mafleming/MultiMod-II/mecrisp-ice-2.7/common-verilog/usb_cdc/usb_cdc.v

//  USB 2.0 full speed Communications Device Class.
//  Written in verilog 2001

// USB_CDC module shall implement Full Speed (12Mbit/s) USB communications device
//   class (or USB CDC class) and Abstract Control Model (ACM) subclass.
// USB_CDC shall implement IN/OUT FIFO interface between USB and external APP module.

module usb_cdc
  #(parameter VENDORID = 16'h0000,
    parameter PRODUCTID = 16'h0000,
    parameter IN_BULK_MAXPACKETSIZE = 'd8,
    parameter OUT_BULK_MAXPACKETSIZE = 'd8,
    parameter BIT_SAMPLES = 'd4,
    parameter USE_APP_CLK = 0,
    parameter APP_CLK_RATIO = 'd4)
   (
    input        clk_i,
    input        rstn_i,

    // ---- to/from Application ------------------------------------
    input        app_clk_i,
    output [7:0] out_data_o,
    output       out_valid_o,
    // While out_valid_o is high, the out_data_o shall be valid and both
    //   out_valid_o and out_data_o shall not change until consumed.
    input        out_ready_i,
    // When both out_valid_o and out_ready_i are high, the out_data_o shall
    //   be consumed.
    input [7:0]  in_data_i,
    input        in_valid_i,
    // While in_valid_i is high, in_data_i shall be valid.
    output       in_ready_o,
    // When both in_ready_o and in_valid_i are high, in_data_i shall
    //   be consumed.

    // ---- to USB bus physical transmitters/receivers --------------
    output       tx_en_o,
    output       tx_dp_o,
    output       tx_dn_o,
    input        rx_dp_i,
    input        rx_dn_i
    );

   localparam    CTRL_MAXPACKETSIZE = 'd8;
   localparam [3:0] ENDP_CTRL = 'd0,
                    ENDP_BULK = 'd1,
                    ENDP_INT = 'd2;

   reg [1:0]        rstn_sq;

   wire [6:0]       addr;
   wire [3:0]       endp;
   wire [7:0]       out_data;
   wire [7:0]       in_data, ctrl_in_data, bulk_in_data;
   wire             out_valid;
   wire             in_req, ctrl_in_req, bulk_in_req;
   wire             in_zlp, ctrl_in_zlp;
   wire             in_valid, ctrl_in_valid, bulk_in_valid;
   wire             out_err;
   wire             out_nak, bulk_out_nak;
   wire             setup;
   wire             stall, ctrl_stall;
   wire             in_toggle_reset;
   wire             out_toggle_reset;
   wire             rstn, usb_reset;
   wire             in_ready, ctrl_in_ready, bulk_in_ready;
   wire             out_ready, ctrl_out_ready, bulk_out_ready;

   assign rstn = rstn_sq[0] & ~usb_reset;
   assign ctrl_in_ready = (endp == ENDP_CTRL) ? in_ready : 1'b0;
   assign ctrl_out_ready = (endp == ENDP_CTRL) ? out_ready : 1'b0;
   assign bulk_in_ready = (endp == ENDP_BULK) ? in_ready : 1'b0;
   assign bulk_out_ready = (endp == ENDP_BULK) ? out_ready : 1'b0;
   assign ctrl_in_req = (endp == ENDP_CTRL) ? in_req : 1'b0;
   assign bulk_in_req = (endp == ENDP_BULK) ? in_req : 1'b0;
   assign in_data = (endp == ENDP_CTRL) ? ctrl_in_data : bulk_in_data;
   assign in_zlp = (endp == ENDP_CTRL) ? ctrl_in_zlp : 1'b0;
   assign in_valid = (endp == ENDP_CTRL) ? ctrl_in_valid : ((endp == ENDP_BULK) ? bulk_in_valid : 1'b0);
   assign stall = (endp == ENDP_CTRL) ? ctrl_stall : 1'b0;
   assign out_nak = (endp == ENDP_BULK) ? bulk_out_nak : 1'b0;

   always @(posedge clk_i or negedge rstn_i) begin
      if (~rstn_i) begin
         rstn_sq <= 2'd0;
      end else begin
         rstn_sq <= {1'b1, rstn_sq[1]};
      end
   end

   sie #(.CTRL_MAXPACKETSIZE(CTRL_MAXPACKETSIZE),
         .IN_BULK_MAXPACKETSIZE(IN_BULK_MAXPACKETSIZE),
         .ENDP_CTRL(ENDP_CTRL),
         .ENDP_BULK(ENDP_BULK),
         .BIT_SAMPLES(BIT_SAMPLES))
   u_sie (.usb_reset_o(usb_reset),
          .tx_en_o(tx_en_o),
          .tx_dp_o(tx_dp_o),
          .tx_dn_o(tx_dn_o),
          .endp_o(endp),
       // .frame_o(),
          .out_data_o(out_data),
          .out_valid_o(out_valid),
          .out_err_o(out_err),
          .in_req_o(in_req),
          .setup_o(setup),
          .out_ready_o(out_ready),
          .in_ready_o(in_ready),
          .clk_i(clk_i),
          .rstn_i(rstn_sq[0]),
          .rx_dp_i(rx_dp_i),
          .rx_dn_i(rx_dn_i),
          .addr_i(addr),
          .in_valid_i(in_valid),
          .in_data_i(in_data),
          .in_zlp_i(in_zlp),
          .out_nak_i(out_nak),
          .stall_i(stall),
          .in_toggle_reset_i(in_toggle_reset),
          .out_toggle_reset_i(out_toggle_reset));

   ctrl_endp #(.VENDORID(VENDORID),
               .PRODUCTID(PRODUCTID),
               .CTRL_MAXPACKETSIZE(CTRL_MAXPACKETSIZE),
               .IN_BULK_MAXPACKETSIZE(IN_BULK_MAXPACKETSIZE),
               .OUT_BULK_MAXPACKETSIZE(OUT_BULK_MAXPACKETSIZE),
               .ENDP_BULK(ENDP_BULK),
               .ENDP_INT(ENDP_INT))
   u_ctrl_endp (.addr_o(addr),
                .in_data_o(ctrl_in_data),
                .in_zlp_o(ctrl_in_zlp),
                .in_valid_o(ctrl_in_valid),
                .stall_o(ctrl_stall),
                .in_toggle_reset_o(in_toggle_reset),
                .out_toggle_reset_o(out_toggle_reset),
                .clk_i(clk_i),
                .rstn_i(rstn),
                .out_data_i(out_data),
                .out_valid_i(out_valid),
                .out_err_i(out_err),
                .in_req_i(ctrl_in_req),
                .setup_i(setup),
                .out_ready_i(ctrl_out_ready),
                .in_ready_i(ctrl_in_ready));

   bulk_endp #(.IN_BULK_MAXPACKETSIZE(IN_BULK_MAXPACKETSIZE),
               .OUT_BULK_MAXPACKETSIZE(OUT_BULK_MAXPACKETSIZE),
               .BIT_SAMPLES(BIT_SAMPLES),
               .USE_APP_CLK(USE_APP_CLK),
               .APP_CLK_RATIO(APP_CLK_RATIO))
   u_bulk_endp (.in_data_o(bulk_in_data),
                .in_valid_o(bulk_in_valid),
                .app_in_ready_o(in_ready_o),
                .out_nak_o(bulk_out_nak),
                .app_out_valid_o(out_valid_o),
                .app_out_data_o(out_data_o),
                .clk_i(clk_i),
                .app_clk_i(app_clk_i),
                .rstn_i(rstn),
                .out_data_i(out_data),
                .out_valid_i(out_valid),
                .out_err_i(out_err),
                .in_req_i(bulk_in_req),
                .app_in_data_i(in_data_i),
                .app_in_valid_i(in_valid_i),
                .out_ready_i(bulk_out_ready),
                .in_ready_i(bulk_in_ready),
                .app_out_ready_i(out_ready_i));
endmodule
