mafleming/MultiMod-II/mecrisp-ice-2.7/multimod2/icestorm/j1a.v

`default_nettype none

`include "../common-verilog/j1-universal-16kb-quickstore.v"

`include "../common-verilog/usb_cdc/usb_cdc.v"
`include "../common-verilog/usb_cdc/bulk_endp.v"
`include "../common-verilog/usb_cdc/ctrl_endp.v"
`include "../common-verilog/usb_cdc/phy_rx.v"
`include "../common-verilog/usb_cdc/phy_tx.v"
`include "../common-verilog/usb_cdc/sie.v"

module top (
    input  clki,     // 48 MHz clock input
    output clki_en,  // Enable external clock

    inout  data_0, // Four user pins
    inout  data_1,
    inout  data_2,
    inout  data_3,

    output rgb0, // LED outputs
    output rgb1,
    output rgb2,

    output spi_cs,    // SPI Flash
    output spi_clk,
    inout  spi_miso,
    inout  spi_mosi,
    inout  spi_io2,
    inout  spi_io3,

    inout  usb_dp, // USB pins
    inout  usb_dn,
    output usb_dp_pu,
    input  usb_activ,

    output to71,   // Tristate buffer control
    output from71,
    output ctrl71,

    input  din71,  // HP71B bus control signals
    input  cdn71,
    input  strn71
);

  // ######   Clock   #########################################

  reg [1:0] divider;

  always @(posedge clki) divider <= divider + 1;

  wire clk_usb = clki;       // 48 MHz
  wire clk     = divider[1]; // 12 MHz

  assign clki_en = 1'b1;


  // ######   Reset logic   ###################################

  wire button = 1'b1;

  reg [7:0] reset_cnt = 0;
  wire resetq = &reset_cnt;

  always @(posedge clk) begin
    if (button) reset_cnt <= reset_cnt + !resetq;
    else        reset_cnt <= 0;
  end

  // ######   Bus   ###########################################

  wire io_rd, io_wr;
  wire [15:0] io_addr;
  wire [15:0] io_dout;
  wire [15:0] io_din;

  reg interrupt = 0;

  // ######   Processor   #####################################

  j1 #( .MEMWORDS(7680) ) _j1( // 15 kb Memory

    .clk(clk),
    .resetq(resetq),

    .io_rd(io_rd),
    .io_wr(io_wr),
    .io_dout(io_dout),
    .io_din(io_din),
    .io_addr(io_addr),

    .interrupt_request(interrupt)
  );

  // ######   SPI   ###########################################
  // M. Fleming
  // Make the SPI IO0~IO3 lines directional

  reg  [3:0] spio_dir = 4'b1110;   // 1:output, 0:input
  reg  [3:0] spio_out;
  wire [3:0] spio_in;

  SB_IO #(.PIN_TYPE(6'b1010_01)) spio0 (.PACKAGE_PIN(spi_miso), .D_OUT_0(spio_out[0]), .D_IN_0(spio_in[0]), .OUTPUT_ENABLE(spio_dir[0]));
  SB_IO #(.PIN_TYPE(6'b1010_01)) spio1 (.PACKAGE_PIN(spi_mosi), .D_OUT_0(spio_out[1]), .D_IN_0(spio_in[1]), .OUTPUT_ENABLE(spio_dir[1]));
  SB_IO #(.PIN_TYPE(6'b1010_01)) spio2 (.PACKAGE_PIN(spi_io2), .D_OUT_0(spio_out[2]), .D_IN_0(spio_in[2]), .OUTPUT_ENABLE(spio_dir[2]));
  SB_IO #(.PIN_TYPE(6'b1010_01)) spio3 (.PACKAGE_PIN(spi_io3), .D_OUT_0(spio_out[3]), .D_IN_0(spio_in[3]), .OUTPUT_ENABLE(spio_dir[3]));

  // ######   Warm Boot Control   #############################
  // M. Fleming
  // Add control register to j1a address space

   reg [2:0] BOOTCTL = 0;

  SB_WARMBOOT B_WARMBOOT(
      .BOOT(BOOTCTL[2]),
      .S0(BOOTCTL[0]),
      .S1(BOOTCTL[1])
  );


  // ######   HP-71B Bus Control   ############################
  // M. Fleming
  // No need to add control signals to j1a address space
  // Buffers are controlled by HP-71B bus state machine

   wire [2:0] BUFCTRL = 0;
   assign BUFCTRL = {to71, from71, ctrl71};


  // ######   HP-71B Bank Control   ###########################
  // M. Fleming
  // Bank control registers selected by the lower three I/O
  // address bits and enabled by the I/O address bit 10   assign read_bank = {inuse, chain, type[1:0]};

  // Bank bits are: InUse, ChainEnd, ROMtype[1:0]
   reg [3:0]  bank0 = 0;
   reg [3:0]  bank1 = 0;
   reg [3:0]  bank2 = 0;
   reg [3:0]  bank3 = 0;
   reg [3:0]  bank4 = 0;
   reg [3:0]  bank5 = 0;
   reg [3:0]  bank6 = 0;
   reg [3:0]  bank7 = 0;


   
  // ######   Ticks   #########################################

  reg [15:0] ticks;

  wire [16:0] ticks_plus_1 = ticks + 1;

  always @(posedge clk)
    if (io_wr & io_addr[14])
      ticks <= io_dout;
    else
      ticks <= ticks_plus_1;

  always @(posedge clk) // Generate interrupt on ticks overflow
    interrupt <= ticks_plus_1[16];

  // ######   Cycles   ########################################

  reg [15:0] cycles;

  always @(posedge clk) cycles <= cycles + 1;

  // ######   DATA   ##########################################
  // M. Fleming
  // These are currently controlled by the j1a CPU but will
  // eventually be part of the HP-71B bus state machine

  reg  [3:0] data_dir;   // 1:output, 0:input
  reg  [3:0] data_out;
  wire [3:0] data_in;

  SB_IO #(.PIN_TYPE(6'b1010_01)) io0 (.PACKAGE_PIN(data_0), .D_OUT_0(data_out[0]), .D_IN_0(data_in[0]), .OUTPUT_ENABLE(data_dir[0]));
  SB_IO #(.PIN_TYPE(6'b1010_01)) io1 (.PACKAGE_PIN(data_1), .D_OUT_0(data_out[1]), .D_IN_0(data_in[1]), .OUTPUT_ENABLE(data_dir[1]));
  SB_IO #(.PIN_TYPE(6'b1010_01)) io2 (.PACKAGE_PIN(data_2), .D_OUT_0(data_out[2]), .D_IN_0(data_in[2]), .OUTPUT_ENABLE(data_dir[2]));
  SB_IO #(.PIN_TYPE(6'b1010_01)) io3 (.PACKAGE_PIN(data_3), .D_OUT_0(data_out[3]), .D_IN_0(data_in[3]), .OUTPUT_ENABLE(data_dir[3]));

  // ######   SRAM   ##########################################

  reg  [15:0] sram_addr;

  wire sram_wr = io_wr & io_addr[7];

  wire [15:0] sram_in_bank0, sram_in_bank1, sram_in_bank2, sram_in_bank3;

    SB_SPRAM256KA rambank0 (
        .DATAIN(io_dout),
        .ADDRESS(sram_addr[13:0]),
        .MASKWREN(4'b1111),
        .WREN(sram_wr),
        .CHIPSELECT(1'b1),
        .CLOCK(clk),
        .STANDBY(1'b0),
        .SLEEP(~(sram_addr[15:14] == 2'b00)),
        .POWEROFF(1'b1),
        .DATAOUT(sram_in_bank0)
);

    SB_SPRAM256KA rambank1 (
        .DATAIN(io_dout),
        .ADDRESS(sram_addr[13:0]),
        .MASKWREN(4'b1111),
        .WREN(sram_wr),
        .CHIPSELECT(1'b1),
        .CLOCK(clk),
        .STANDBY(1'b0),
        .SLEEP(~(sram_addr[15:14] == 2'b01)),
        .POWEROFF(1'b1),
        .DATAOUT(sram_in_bank1)
);

    SB_SPRAM256KA rambank2 (
        .DATAIN(io_dout),
        .ADDRESS(sram_addr[13:0]),
        .MASKWREN(4'b1111),
        .WREN(sram_wr),
        .CHIPSELECT(1'b1),
        .CLOCK(clk),
        .STANDBY(1'b0),
        .SLEEP(~(sram_addr[15:14] == 2'b10)),
        .POWEROFF(1'b1),
        .DATAOUT(sram_in_bank2)
);

    SB_SPRAM256KA rambank3 (
        .DATAIN(io_dout),
        .ADDRESS(sram_addr[13:0]),
        .MASKWREN(4'b1111),
        .WREN(sram_wr),
        .CHIPSELECT(1'b1),
        .CLOCK(clk),
        .STANDBY(1'b0),
        .SLEEP(~(sram_addr[15:14] == 2'b11)),
        .POWEROFF(1'b1),
        .DATAOUT(sram_in_bank3)
);

  wire [15:0] sram_in = sram_in_bank3 | sram_in_bank2 | sram_in_bank1 | sram_in_bank0;

  // ######   USB-CDC terminal   ##############################

  assign usb_dp_pu = resetq;     // Pull-up on USB-P
   
  wire usb_p_tx;
  wire usb_n_tx;
  wire usb_p_rx;
  wire usb_n_rx;
  wire usb_tx_en;

   SB_IO #(
       .PIN_TYPE(6'b 1010_01), // PIN_OUTPUT_TRISTATE - PIN_INPUT
       .PULLUP(1'b 0)
   ) iobuf_usbp (
       .PACKAGE_PIN(usb_dp),
       .OUTPUT_ENABLE(usb_tx_en),
       .D_OUT_0(usb_p_tx),
       .D_IN_0(usb_p_rx)
   );

   SB_IO #(
       .PIN_TYPE(6'b 1010_01), // PIN_OUTPUT_TRISTATE - PIN_INPUT
       .PULLUP(1'b 0)
   ) iobuf_usbn (
       .PACKAGE_PIN(usb_dn),
       .OUTPUT_ENABLE(usb_tx_en),
       .D_OUT_0(usb_n_tx),
       .D_IN_0(usb_n_rx)
   );

  usb_cdc #(.VENDORID(16'h0483), .PRODUCTID(16'h5740), .BIT_SAMPLES(4), .USE_APP_CLK(1), .APP_CLK_RATIO(4)) _terminal
  (
    // Part running on 48 MHz:

    .clk_i(clk_usb),
    .tx_en_o(usb_tx_en),
    .tx_dp_o(usb_p_tx),
    .tx_dn_o(usb_n_tx),
    .rx_dp_i(usb_p_rx),
    .rx_dn_i(usb_n_rx),

    // Part running on 12 MHz:

    .app_clk_i(clk),
    .rstn_i(resetq),

    .out_data_o(terminal_data),
    .out_valid_o(terminal_valid),
    .out_ready_i(terminal_rd),

    .in_data_i(io_dout[7:0]),
    .in_ready_o(terminal_ready),
    .in_valid_i(terminal_wr)
  );

  wire terminal_valid, terminal_ready;
  wire [7:0] terminal_data;
  wire terminal_wr = io_wr & io_addr[12];
  wire terminal_rd = io_rd & io_addr[12];

  // ######   RING OSCILLATOR   ###############################

  wire [1:0] buffers_in, buffers_out;
  assign buffers_in = {buffers_out[0:0], ~buffers_out[1]};
  SB_LUT4 #(
          .LUT_INIT(16'd2)
  ) buffers [1:0] (
          .O(buffers_out),
          .I0(buffers_in),
          .I1(1'b0),
          .I2(1'b0),
          .I3(1'b0)
  );

  wire random = ~buffers_out[1];

  // ######   Blink   #########################################

  // Instantiate iCE40 LED driver hard logic.
  //
  // Note that it's possible to drive the LEDs directly,
  // however that is not current-limited and results in
  // overvolting the red LED.
  //
  // See also:
  // https://www.latticesemi.com/-/media/LatticeSemi/Documents/ApplicationNotes/IK/ICE40LEDDriverUsageGuide.ashx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

  reg [2:0] LEDS;

  SB_RGBA_DRV #(
      .CURRENT_MODE("0b1"),       // half current
      .RGB0_CURRENT("0b000011"),  // 4 mA
      .RGB1_CURRENT("0b000011"),  // 4 mA
      .RGB2_CURRENT("0b000011")   // 4 mA
  ) RGBA_DRIVER (
      .CURREN(1'b1),
      .RGBLEDEN(1'b1),
      .RGB1PWM(LEDS[0]),     // Red
      .RGB0PWM(LEDS[1]),     // Green
      .RGB2PWM(LEDS[2]),     // Blue
      .RGB0(rgb0),
      .RGB1(rgb1),
      .RGB2(rgb2)
  );


  // ######   IO Ports   ######################################

  /*        Bit READ            WRITE

    + ...0                      Write as usual
    + ...1                      _C_lear bits
    + ...2                      _S_et bits
    + ...3                      _T_oggle bits

      0008  3   LEDS            LEDS (cst)

      0010  4   IN                          Input
      0020  5   OUT             OUT (cst)   Output
      0040  6   DIR             DIR (cst)   Direction
      0080  7   SRAM read       SRAM write

      0100  8   SPI read        SPI write
      0101                      SPIO direction
      0200  9   USB status      Warm Boot write
      0400  10  Bank control    Bank control
      0800  11  SRAM addr       SRAM addr

      1000  12  UART RX         UART TX
      2000  13  UART Flags
      4000  14  Ticks           Set Ticks
      8000  15  Cycles
  */

  assign io_din =

    (io_addr[ 3] ? {13'd0, LEDS}                                                    : 16'd0) |

    (io_addr[ 4] ? {12'd0, data_in}                                                 : 16'd0) |
    (io_addr[ 5] ? {12'd0, data_out}                                                : 16'd0) |
    (io_addr[ 6] ? { 8'd0, spio_dir, data_dir}                                      : 16'd0) |
    (io_addr[ 7] ?         sram_in                                                  : 16'd0) |

    (io_addr[ 8] ? {12'd0, spio_in}                                                 : 16'd0) |
    (io_addr[ 9] ? {13'd0, usb_activ, usb_p_tx, usb_n_tx}                           : 16'd0) |
/*  Only needed during development */
    ((io_addr[10] & (io_addr[2:0] == 0)) ? {12'd0, bank0}                           : 16'd0) |
    ((io_addr[10] & (io_addr[2:0] == 1)) ? {12'd0, bank1}                           : 16'd0) |
    ((io_addr[10] & (io_addr[2:0] == 2)) ? {12'd0, bank2}                           : 16'd0) |
    ((io_addr[10] & (io_addr[2:0] == 3)) ? {12'd0, bank3}                           : 16'd0) |
    ((io_addr[10] & (io_addr[2:0] == 4)) ? {12'd0, bank4}                           : 16'd0) |
    ((io_addr[10] & (io_addr[2:0] == 5)) ? {12'd0, bank5}                           : 16'd0) |
    ((io_addr[10] & (io_addr[2:0] == 6)) ? {12'd0, bank6}                           : 16'd0) |
    ((io_addr[10] & (io_addr[2:0] == 7)) ? {12'd0, bank7}                           : 16'd0) |
/**/
    (io_addr[11] ?         sram_addr                                                : 16'd0) |

    (io_addr[12] ? { 8'd0, terminal_data}                                           : 16'd0) |
    (io_addr[13] ? {13'd0, random, terminal_valid, terminal_ready}                  : 16'd0) |
    (io_addr[14] ?         ticks                                                    : 16'd0) |
    (io_addr[15] ?         cycles                                                   : 16'd0) ;

  always @(posedge clk) begin

    if (io_wr & io_addr[3] & (io_addr[1:0] == 0))  LEDS  <=           io_dout;
    if (io_wr & io_addr[3] & (io_addr[1:0] == 1))  LEDS  <=  LEDS  & ~io_dout; // Clear
    if (io_wr & io_addr[3] & (io_addr[1:0] == 2))  LEDS  <=  LEDS  |  io_dout; // Set
    if (io_wr & io_addr[3] & (io_addr[1:0] == 3))  LEDS  <=  LEDS  ^  io_dout; // Invert

    if (io_wr & io_addr[5] & (io_addr[1:0] == 0))  data_out  <=               io_dout;
    if (io_wr & io_addr[5] & (io_addr[1:0] == 1))  data_out  <=  data_out  & ~io_dout; // Clear
    if (io_wr & io_addr[5] & (io_addr[1:0] == 2))  data_out  <=  data_out  |  io_dout; // Set
    if (io_wr & io_addr[5] & (io_addr[1:0] == 3))  data_out  <=  data_out  ^  io_dout; // Invert

    if (io_wr & io_addr[6] & (io_addr[1:0] == 0))  data_dir  <=               io_dout;
    if (io_wr & io_addr[6] & (io_addr[1:0] == 1))  data_dir  <=  data_dir  & ~io_dout; // Clear
    if (io_wr & io_addr[6] & (io_addr[1:0] == 2))  data_dir  <=  data_dir  |  io_dout; // Set
    if (io_wr & io_addr[6] & (io_addr[1:0] == 3))  data_dir  <=  data_dir  ^  io_dout; // Invert

    if (io_wr & io_addr[8] & (io_addr[1:0] == 0))  {spi_clk, spi_cs, spio_out}  <= io_dout;
    if (io_wr & io_addr[8] & (io_addr[1:0] == 1))  spio_dir                     <= io_dout;

    if (io_wr & io_addr[9]) BOOTCTL                <= io_dout;
    if (io_wr & io_addr[10] & (io_addr[2:0] == 0)) bank0   <= io_dout;
    if (io_wr & io_addr[10] & (io_addr[2:0] == 1)) bank1   <= io_dout;
    if (io_wr & io_addr[10] & (io_addr[2:0] == 2)) bank2   <= io_dout;
    if (io_wr & io_addr[10] & (io_addr[2:0] == 3)) bank3   <= io_dout;
    if (io_wr & io_addr[10] & (io_addr[2:0] == 4)) bank4   <= io_dout;
    if (io_wr & io_addr[10] & (io_addr[2:0] == 5)) bank5   <= io_dout;
    if (io_wr & io_addr[10] & (io_addr[2:0] == 6)) bank6   <= io_dout;
    if (io_wr & io_addr[10] & (io_addr[2:0] == 7)) bank7   <= io_dout;

    if (io_wr & io_addr[11]) sram_addr <= io_dout;
  end

endmodule
