mafleming/MultiMod-II/mecrisp-ice-2.7/common-verilog/j1-universal-32bit-singleport.v

`default_nettype none

`include "../common-verilog/stack2.v"

module j1(
  input wire clk,
  input wire resetq,

  output wire io_rd,
  output wire io_wr,
  output wire [31:0] io_addr,
  output wire [31:0] io_dout,
  input  wire [31:0] io_din,

  input  wire interrupt_request
);

  parameter MEMBITS   = 13;             // Bit width of memory
  parameter MEMWORDS  = 8192;          // Memory to be addressed with these bits
  parameter IRQOPCODE = 32'h40000001; // Interrupt: Execute "Call 0004"

  // ######   MEMORY   ########################################

    wire [MEMBITS-1:0] code_addr;
    reg  [31:0] insn_from_memory;

    reg [31:0] mem [0:MEMWORDS-1]; initial $readmemh("build/iceimage.hex", mem);

    always @(posedge clk) begin
      if (pcN[29]) mem[code_addr] <= st0N;
      else insn_from_memory <= mem[code_addr];
    end

  // ######   PROCESSOR   #####################################

  reg [4:0] rsp, rspN;          // Return stack pointer
  reg [4:0] dsp, dspN;          // Data stack pointer
  reg [31:0] st0, st0N;         // Top of data stack
  reg dstkW;                    // Data stack write

  reg [31:0] pc, pcN;           // Program Counter. pc[0] is interrupt enable bit.

  wire interrupt_enable = pc[0];
  wire interrupt = interrupt_request & interrupt_enable;

  wire [31:0] insn = interrupt ? IRQOPCODE : insn_from_memory;  // Interrupt: Execute "Call 7FFC"
  wire [31:0] pc_plus_4 = (pc + {29'b0, ~interrupt, 2'b0}) | {interrupt, 31'b0};      // Do not increment PC for interrupts to continue later at the same location. Set MSB on interrupt entries which will be pushed to return stack !
  wire fetch = pc[30] & ~interrupt;                            // Memory fetch data on pc[30] only valid if this is no interrupt entry.
  wire store = pc[29] & ~interrupt;

  reg rstkW;                    // Return stack write
  wire [31:0] rstkD;            // Return stack write value
  reg notreboot = 0;

  assign io_addr = st0[31:0];
  assign code_addr = pcN[MEMBITS+1:2];

  // The D and R stacks
  wire [31:0] st1, rst0;
  reg [1:0] dspI, rspI;

  stack2 #(.DEPTH(32), .WIDTH(32)) rstack(.clk(clk), .rd(rst0), .we(rstkW), .wd(rstkD), .delta(rspI));
  stack2 #(.DEPTH(32), .WIDTH(32)) dstack(.clk(clk), .rd(st1),  .we(dstkW), .wd(st0),   .delta(dspI));

  wire [32:0] minus = {1'b1, ~st0} + st1 + 1;

  wire signedless = st0[31] ^ st1[31] ? st1[31] : minus[32];
  wire unsignedless = minus[32];
  wire zeroflag = minus[31:0] == 0;

  wire [63:0] umstar = st0 * st1;

  always @*
  begin
    // Compute the new value of st0
    casez ({fetch, store, insn[31:29], insn[12:8]})

  //  10'b00_011_00000: st0N = st0;                                   // TOS
      10'b00_011_00001: st0N = st1;                                   // NOS
      10'b00_011_00010: st0N = st0 + st1;                             // +
      10'b00_011_00011: st0N = st0 & st1;                             // and

      10'b00_011_00100: st0N = st0 | st1;                             // or
      10'b00_011_00101: st0N = st0 ^ st1;                             // xor
      10'b00_011_00110: st0N = ~st0;                                  // invert
      10'b00_011_00111: st0N = {32{zeroflag}};                        //  =

      10'b00_011_01000: st0N = {32{signedless}};                      //  <
      10'b00_011_01001: st0N = {st0[31], st0[31:1]};                  // 1 arshift
      10'b00_011_01010: st0N = {st0[30:0], 1'b0};                     // 1 lshift
      10'b00_011_01011: st0N = rst0;                                  // r@

      10'b00_011_01100: st0N = minus[31:0];                           // -
      10'b00_011_01101: st0N = io_din;                                // Read IO
      10'b00_011_01110: st0N = {27'b0, dsp};                          // depth
      10'b00_011_01111: st0N = {32{unsignedless}};                    // u<

  //  10'b00_000_?????: st0N = st0;                                   // Jump
  //  10'b00_010_?????: st0N = st0;                                   // Call

      10'b01_???_?????,                                               // Memory Store,
      10'b00_001_?????: st0N = st1;                                   // Conditional jump

      10'b00_1??_?????: st0N = { 1'b0, insn[30:0] };                  // Literal
      10'b10_???_?????: st0N = insn;                                  // Memory fetch

  // Specials available on HX8K:

      10'b00_011_10000: st0N = st1 << st0;                            // lshift
      10'b00_011_10001: st0N = st1 >> st0;                            // rshift
      10'b00_011_10010: st0N = $signed(st1) >>> st0;                  // arshift
      10'b00_011_10011: st0N = {27'b0, rsp};                          // rdepth

      10'b00_011_10100: st0N = umstar[31:0];                          // Low  um*
      10'b00_011_10101: st0N = umstar[63:32];                         // High um*
      10'b00_011_10110: st0N = st0 + 1;                               // 1+
      10'b00_011_10111: st0N = st0 - 1;                               // 1-

      default: st0N = st0;
    endcase
  end

  wire func_T_N =   (insn[6:4] == 1);
  wire func_T_R =   (insn[6:4] == 2);
//wire func_write = (insn[6:4] == 3);
  wire func_iow =   (insn[6:4] == 4);
  wire func_ior =   (insn[6:4] == 5);
  wire func_dint =  (insn[6:4] == 6);
  wire func_eint =  (insn[6:4] == 7);

  wire is_alu = notreboot & !fetch & (insn[31:29] == 3'b011);

//assign mem_wr = is_alu & func_write;
  assign io_wr  = is_alu & func_iow;
  assign io_rd  = is_alu & func_ior;
  assign io_dout   = st1;

  wire eint = is_alu & func_eint;
  wire dint = is_alu & func_dint;

  wire interrupt_enableN =                   (interrupt_enable | eint) & ~(dint | interrupt); // Disable interrups on IRQ entry.
  wire interrupt_enableN_return = (rst0[31] | interrupt_enable | eint) & ~(dint | interrupt); // Reenable interrupts on return stack MSB.

  // Value which could be written to return stack: Either return address in case of a call or TOS.
  assign rstkD = (insn[29] == 1'b0) ? pc_plus_4 : st0;

  always @*
  begin
    casez ({fetch, store, insn[31:29]})                    // Calculate new data stack pointer
    5'b10_???,                                               // Memory Store,
    5'b00_1??:  {dstkW, dspI} = {1'b1,      2'b01};          // Memory Fetch & Literal

    5'b01_???,
    5'b00_001:  {dstkW, dspI} = {1'b0,      2'b11};          // Store & Conditional jump
    5'b00_011:  {dstkW, dspI} = {func_T_N,  {insn[1:0]}};    // ALU
    default:    {dstkW, dspI} = {1'b0,      2'b00};          // Default: Unchanged
    endcase
    dspN = dsp + {dspI[1], dspI[1], dspI[1], dspI};

    casez ({fetch|store, insn[31:29]})                     // Calculate new return stack pointer
    4'b1_???:   {rstkW, rspI} = {1'b0,      2'b11};          // Memory Fetch or Store, triggered by high address bit set
    4'b0_010:   {rstkW, rspI} = {1'b1,      2'b01};          // Call
    4'b0_011:   {rstkW, rspI} = {func_T_R,  insn[3:2]};      // ALU
    default:    {rstkW, rspI} = {1'b0,      2'b00};          // Default: Unchanged
    endcase
    rspN = rsp + {rspI[1], rspI[1], rspI[1], rspI};

    casez ({notreboot, fetch|store, insn[31:29], insn[7], |st0})   // New address for PC
    7'b0_0_???_?_?:   pcN = 0;                                     // Boot: Start at address zero with interrupts disabled
    7'b1_0_000_?_?,
    7'b1_0_010_?_?,
    7'b1_0_001_?_0:   pcN = {1'b0, insn[28:0], 1'b0, interrupt_enableN};        // Jumps & Calls: Destination address
    7'b1_1_???_?_?,                                                             // Memory Fetch or Store
    7'b1_0_011_1_?:   pcN = {1'b0, rst0[30:2], 1'b0, interrupt_enableN_return}; // ALU+exit: Return. Maybe reenable interrupts.
    default:          pcN = { pc_plus_4[31:2], 1'b0, interrupt_enableN};        // Default: Increment PC to next opcode
    endcase
  end

  always @(negedge resetq or posedge clk)
  begin
    if (!resetq) begin
      notreboot <= 0;
      { pc, dsp, rsp, st0 } <= 0;
    end else begin
      notreboot <= 1;
      { pc, dsp, rsp, st0 }  <= { pcN, dspN, rspN, st0N };
    end
  end

endmodule
