mafleming/MultiMod-II/mecrisp-ice-2.7/common-verilog/uart.v

/*
 *  PicoSoC - A simple example SoC using PicoRV32
 *
 *  Copyright (C) 2017  Clifford Wolf <clifford@clifford.at>
 *
 *  Permission to use, copy, modify, and/or distribute this software for any
 *  purpose with or without fee is hereby granted, provided that the above
 *  copyright notice and this permission notice appear in all copies.
 *
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
 */

 // October 2019, Matthias Koch: Renamed wires

module buart (
    input clk,
    input resetq,

    output tx,
    input  rx,

    input  wr,
    input  rd,
    input  [7:0] tx_data,
    output [7:0] rx_data,

    output busy,
    output valid
);

    reg [3:0] recv_state;
    reg [$clog2(`cfg_divider)-1:0] recv_divcnt;   // Counts to cfg_divider. Reserve enough bytes !
    reg [7:0] recv_pattern;
    reg [7:0] recv_buf_data;
    reg recv_buf_valid;

    reg [9:0] send_pattern;
    reg [3:0] send_bitcnt;
    reg [$clog2(`cfg_divider)-1:0] send_divcnt;   // Counts to cfg_divider. Reserve enough bytes !
    reg send_dummy;

    assign rx_data = recv_buf_data;
    assign valid = recv_buf_valid;
    assign busy = (send_bitcnt || send_dummy);

    always @(posedge clk) begin
        if (!resetq) begin

            recv_state <= 0;
            recv_divcnt <= 0;
            recv_pattern <= 0;
            recv_buf_data <= 0;
            recv_buf_valid <= 0;

        end else begin
            recv_divcnt <= recv_divcnt + 1;

            if (rd) recv_buf_valid <= 0;

            case (recv_state)
                0: begin
                    if (!rx)
                        recv_state <= 1;
                    recv_divcnt <= 0;
                end
                1: begin
                    if (2*recv_divcnt > `cfg_divider) begin
                        recv_state <= 2;
                        recv_divcnt <= 0;
                    end
                end
                10: begin
                    if (recv_divcnt > `cfg_divider) begin
                        recv_buf_data <= recv_pattern;
                        recv_buf_valid <= 1;
                        recv_state <= 0;
                    end
                end
                default: begin
                    if (recv_divcnt > `cfg_divider) begin
                        recv_pattern <= {rx, recv_pattern[7:1]};
                        recv_state <= recv_state + 1;
                        recv_divcnt <= 0;
                    end
                end
            endcase
        end
    end

    assign tx = send_pattern[0];

    always @(posedge clk) begin
        send_divcnt <= send_divcnt + 1;
        if (!resetq) begin
            send_pattern <= ~0;
            send_bitcnt <= 0;
            send_divcnt <= 0;
            send_dummy <= 1;
        end else begin
            if (send_dummy && !send_bitcnt) begin
                send_pattern <= ~0;
                send_bitcnt <= 15;
                send_divcnt <= 0;
                send_dummy <= 0;
            end else
            if (wr && !send_bitcnt) begin
                send_pattern <= {1'b1, tx_data[7:0], 1'b0};
                send_bitcnt <= 10;
                send_divcnt <= 0;
            end else
            if (send_divcnt > `cfg_divider && send_bitcnt) begin
                send_pattern <= {1'b1, send_pattern[9:1]};
                send_bitcnt <= send_bitcnt - 1;
                send_divcnt <= 0;
            end
        end
    end
endmodule
